jesodium/WRO2026/arduino-mega/ref-images/L293D-Shield-DC-Motor-Connections.jpg

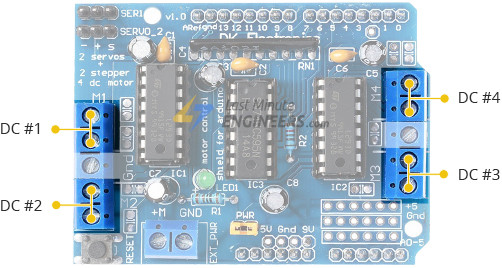
arduino-mega/ref-images/L293D-Shield-DC-Motor-Connections.jpg
