jesodium/WRO2026/arduino-mega/ref-images/L293D-Shield-Pin-Correlation.webp

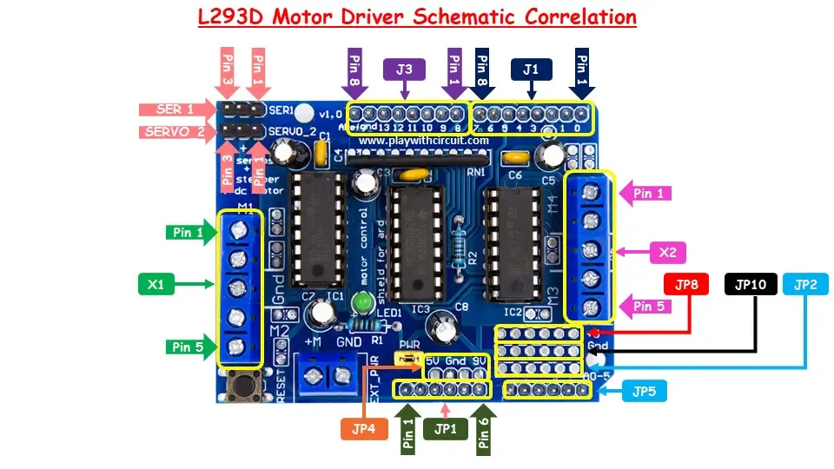
arduino-mega/ref-images/L293D-Shield-Pin-Correlation.webp
