jesodium/WRO2026/arduino-mega/ref-images/L293D-Shield-Power-Supply.jpg

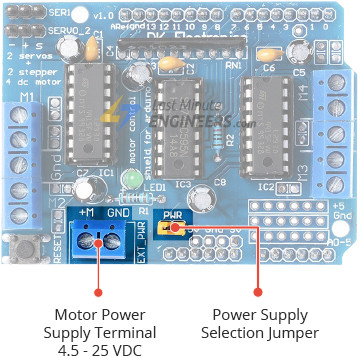
arduino-mega/ref-images/L293D-Shield-Power-Supply.jpg
