jesodium/WRO2026/docs/code-shots/1-mega-sensors.png

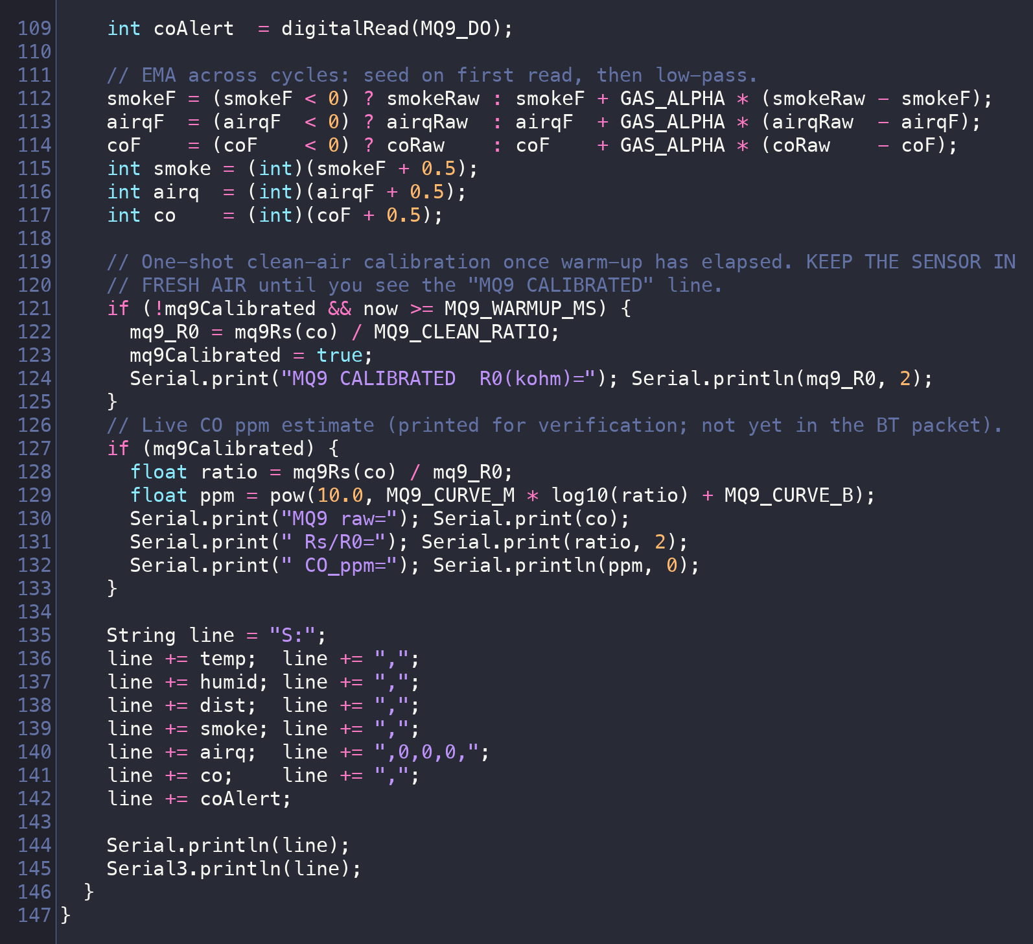
docs/code-shots/1-mega-sensors.png
